conejoninja/arcade/assets/usbasp3.png

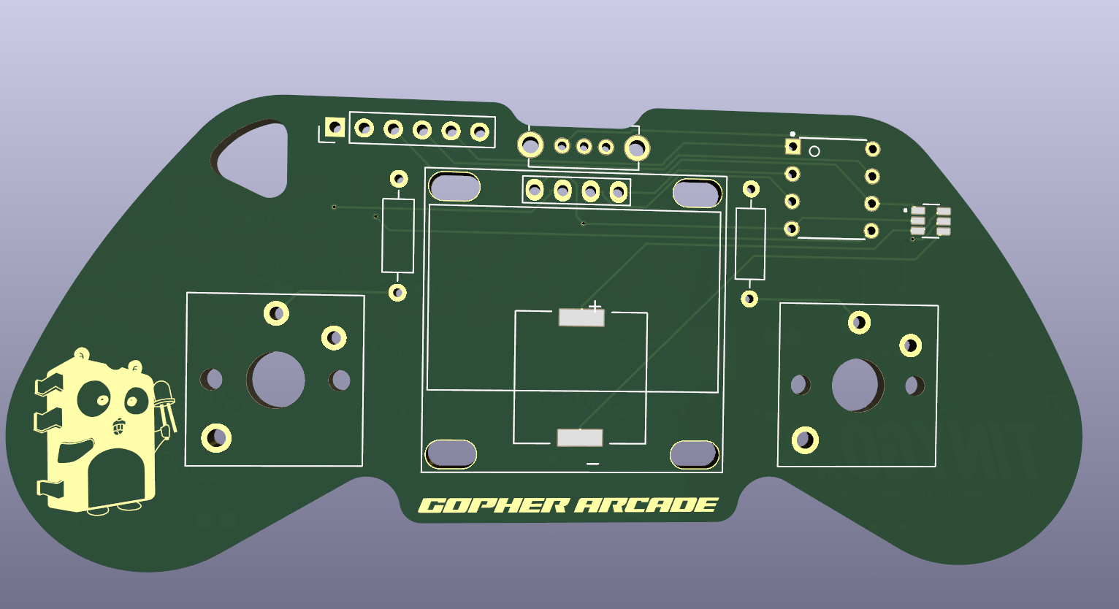
assets/usbasp3.png
