conejoninja/arcade/hardware/kicad/gopher-arcade/gopher-arcade.kicad_sch

## KiCad design hardware/kicad/gopher-arcade/gopher-arcade.kicad_sch (2025-09-09)

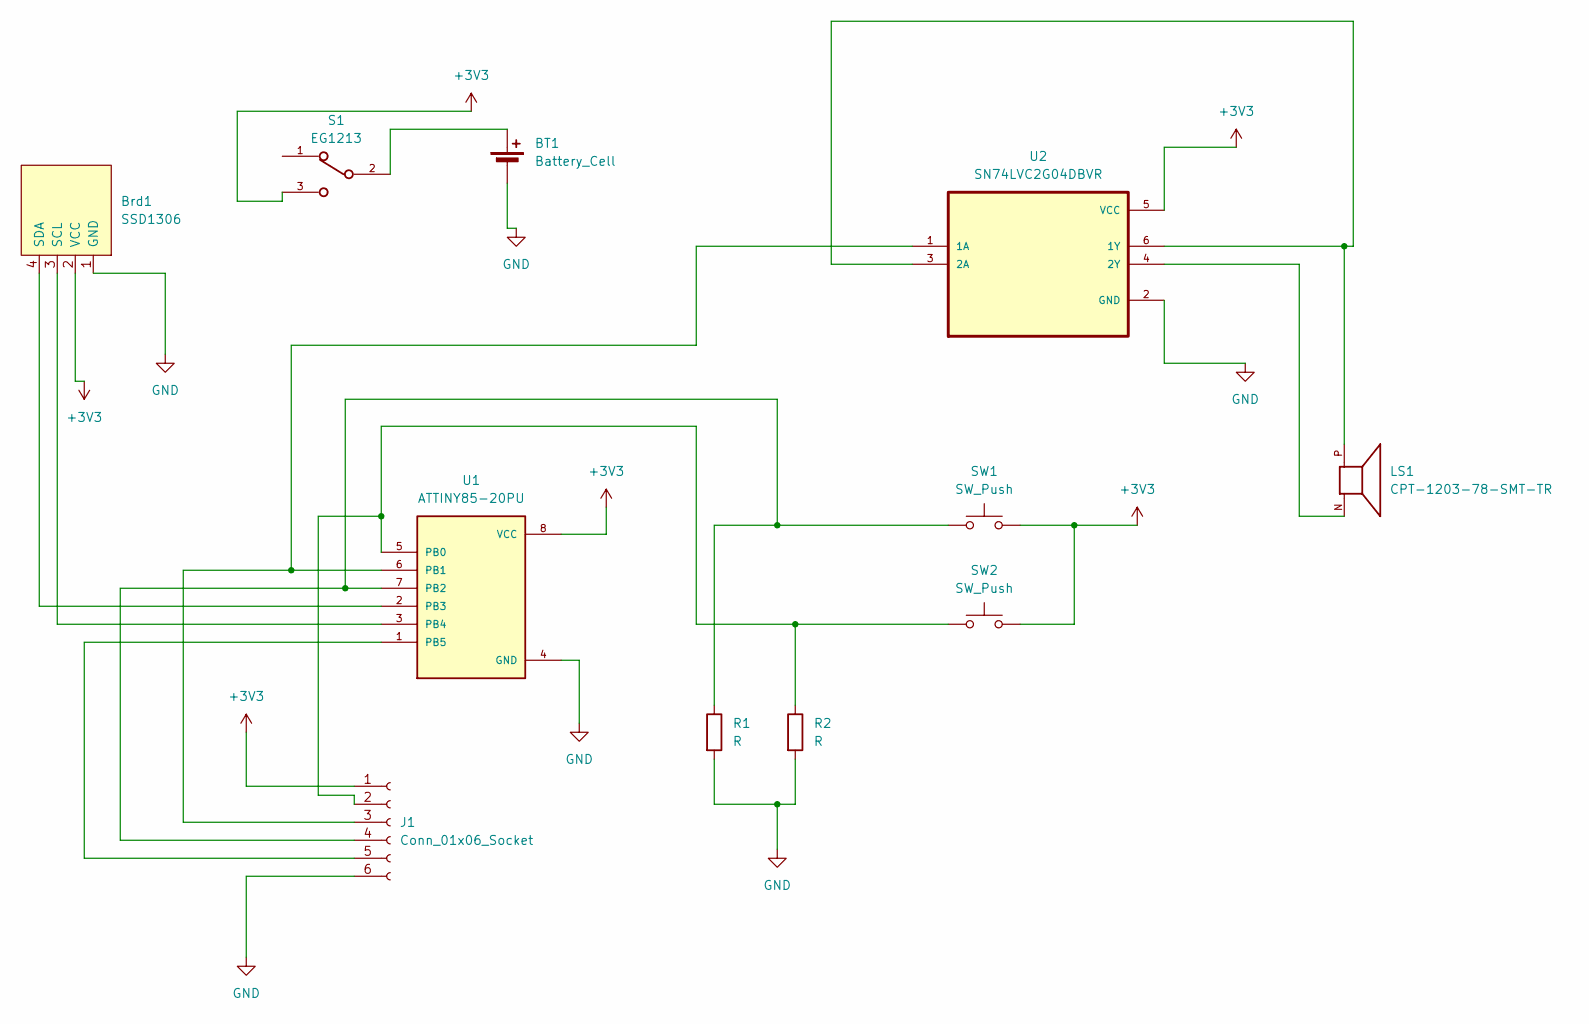
[picture p11: schematic gopher-arcade.kicad_sch]

Parts:
BT1: Battery_Cell; BatteryHolder_Multicomp_BC-2001_1x2032
Brd1: SSD1306; 128x64OLED
J1: Conn_01x06_Socket; PinHeader_1x06_P2.54mm_Vertical
LS1: CPT-1203-78-SMT-TR; XDCR_CPT-1203-78-SMT-TR; PARTREV 1.0
R1, R2: R; R_Axial_DIN0207_L6.3mm_D2.5mm_P10.16mm_Horizontal
S1: EG1213; SW_EG1213
SW1, SW2: SW_Push; SW_Kailh_Choc_V1V2
U1: ATTINY85-20PU; DIP762W46P254L927H533Q8B
U2: SN74LVC2G04DBVR; SOT95P280X145-6N; DigiKey_Part_Number 296-13261-1-ND

Connections:
+3V3: Brd1.2 (VCC), J1.1, S1.3, SW1.2, SW2.2, U1.8 (VCC), U2.5 (VCC)
GND: BT1.2 (-), Brd1.1 (GND), J1.6, R1.2, R2.2, U1.4 (GND), U2.2 (GND)
unnamed: BT1.1 (+), S1.2
unnamed: Brd1.3 (SCL), U1.3 (PB4)
unnamed: Brd1.4 (SDA), U1.2 (PB3)
unnamed: J1.2, R2.1, SW2.1, U1.5 (PB0)
unnamed: J1.3, U1.6 (PB1), U2.1 (1A)
unnamed: J1.4, R1.1, SW1.1, U1.7 (PB2)
unnamed: J1.5, U1.1 (PB5)
unnamed: LS1.N, U2.4 (2Y)
unnamed: LS1.P, U2.3 (2A), U2.6 (1Y)
